mattybrad/drumkid/docs/v6/photos/monochrome/IMG_20201204_124251521.jpg

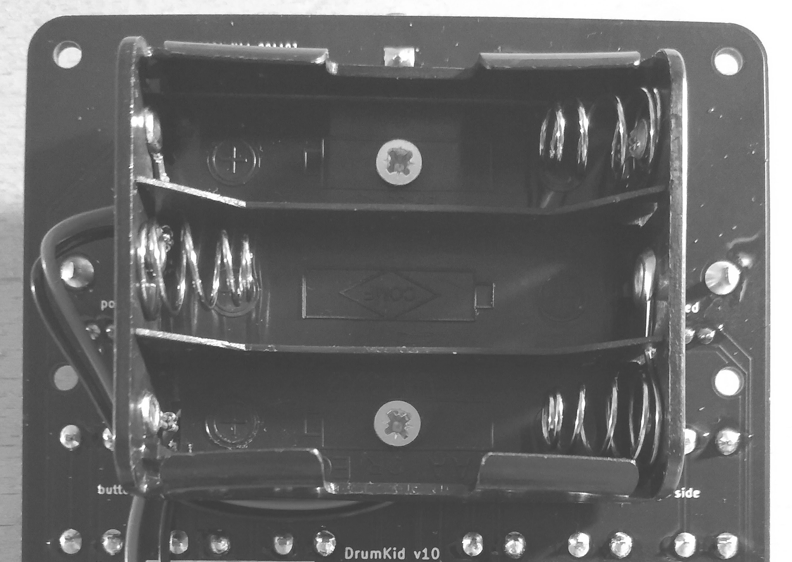
docs/v6/photos/monochrome/IMG_20201204_124251521.jpg
