mattybrad/drumkid/docs/v6/photos/monochrome/IMG_20201204_130344814.jpg

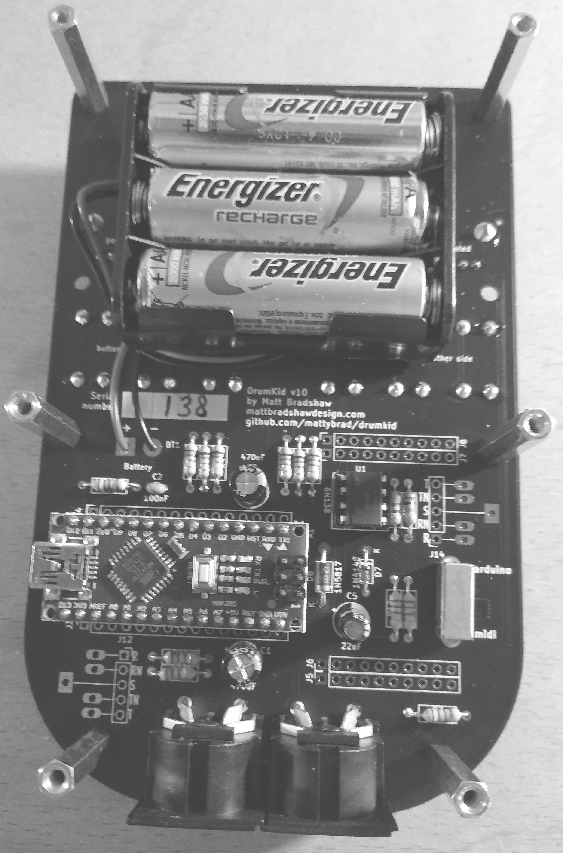
docs/v6/photos/monochrome/IMG_20201204_130344814.jpg
