mattybrad/drumkid/docs/v6/photos/monochrome/IMG_20201204_140902341.jpg

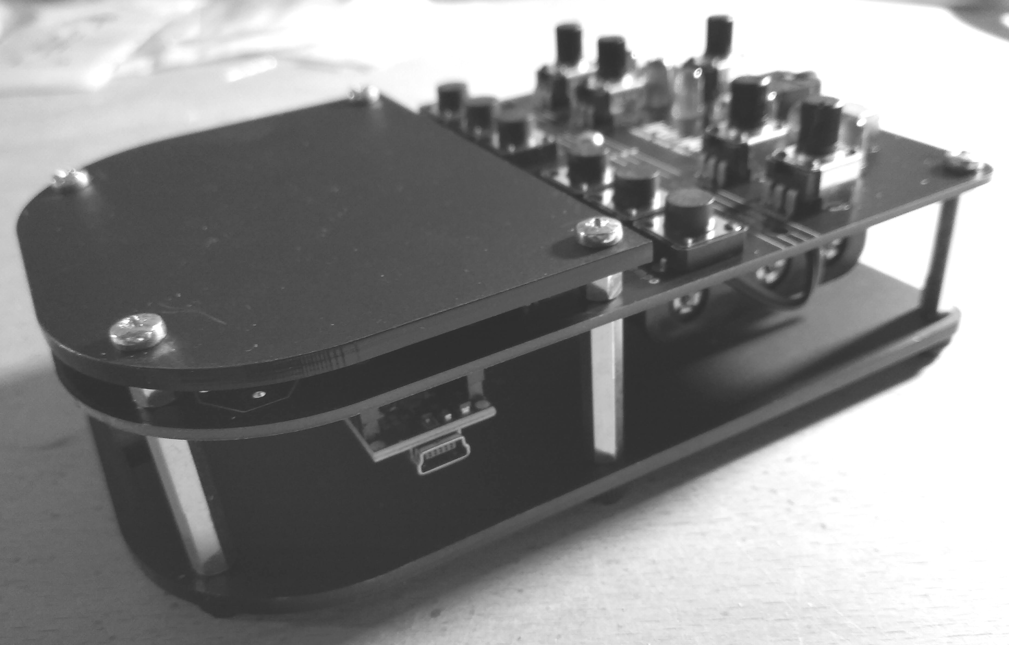
docs/v6/photos/monochrome/IMG_20201204_140902341.jpg
