mattybrad/drumkid/misc/jig/underside.png

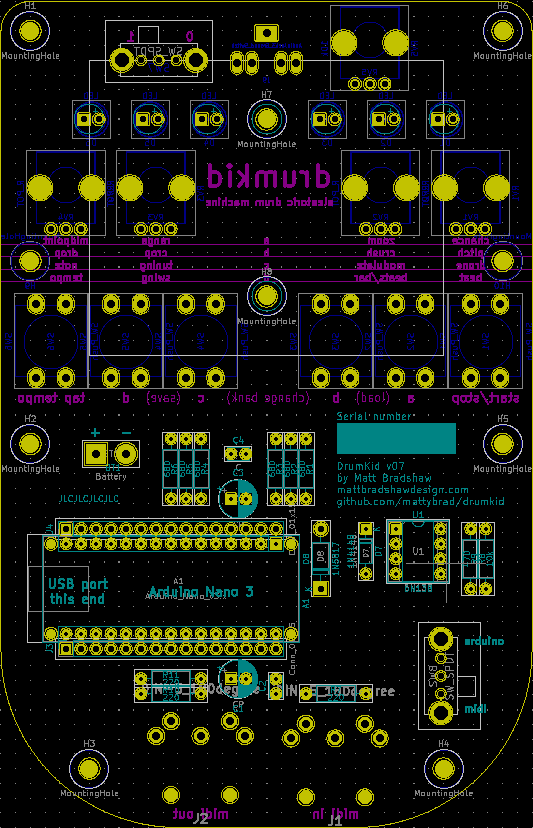
misc/jig/underside.png
