mattybrad/drumkid/case/drumkid_v3_cover.stl

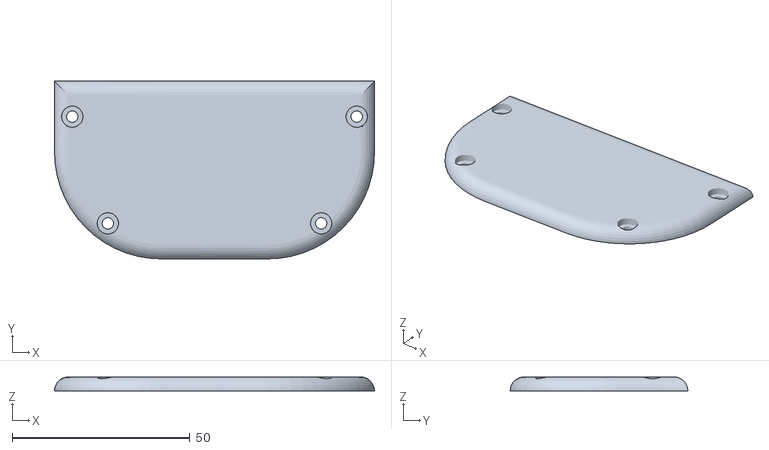
[picture p23: CAD file, 2019-08-09]
case/drumkid_v3_cover.stl
90.0 x 50.0 x 4.00
