mattybrad/drumkid/case/v6/drumkid laser parts.dxf

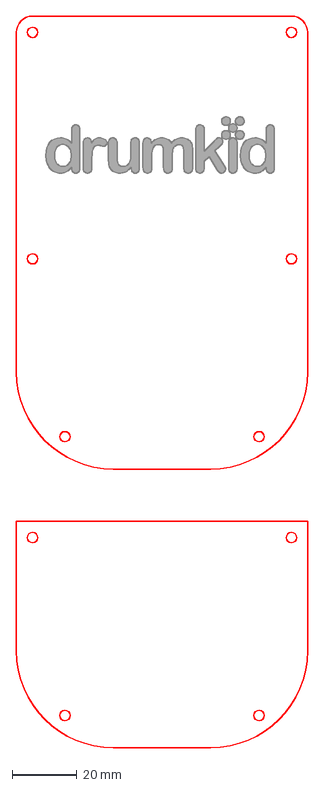
[picture p24: CAD file, 2021-01-12]
case/v6/drumkid laser parts.dxf
90.0 x 226.2 mm
