mattybrad/drumkid/case/drumkid laser parts v2.dxf

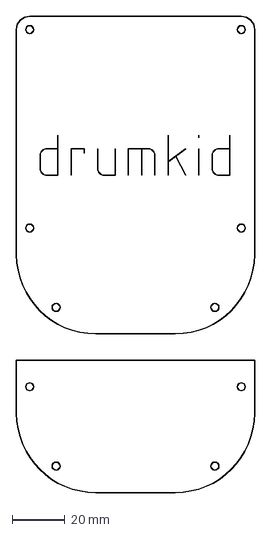
[picture p25: CAD file, 2019-08-09]
case/drumkid laser parts v2.dxf
90.0 x 180.0 mm
