mattybrad/drumkid/case/v6/drumkid laser parts 600x600.dxf

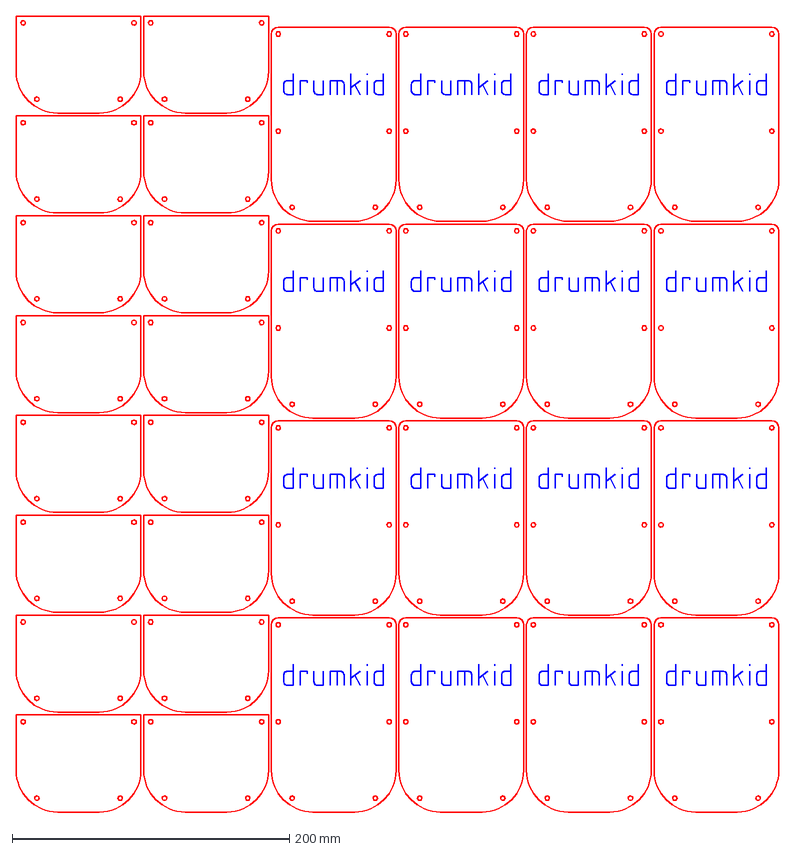
[picture p26: CAD file, 2020-04-07]
case/v6/drumkid laser parts 600x600.dxf
550.0 x 574.0 mm
