mattybrad/drumkid/case/v3 cover.FCStd

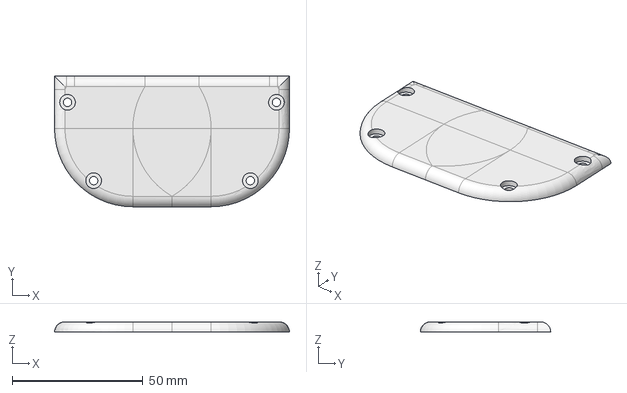
[picture p27: CAD file, 2019-08-09]
case/v3 cover.FCStd
90.0 x 50.0 x 4.00 mm
