mattybrad/drumkid/misc/jig/jig_underside.FCStd

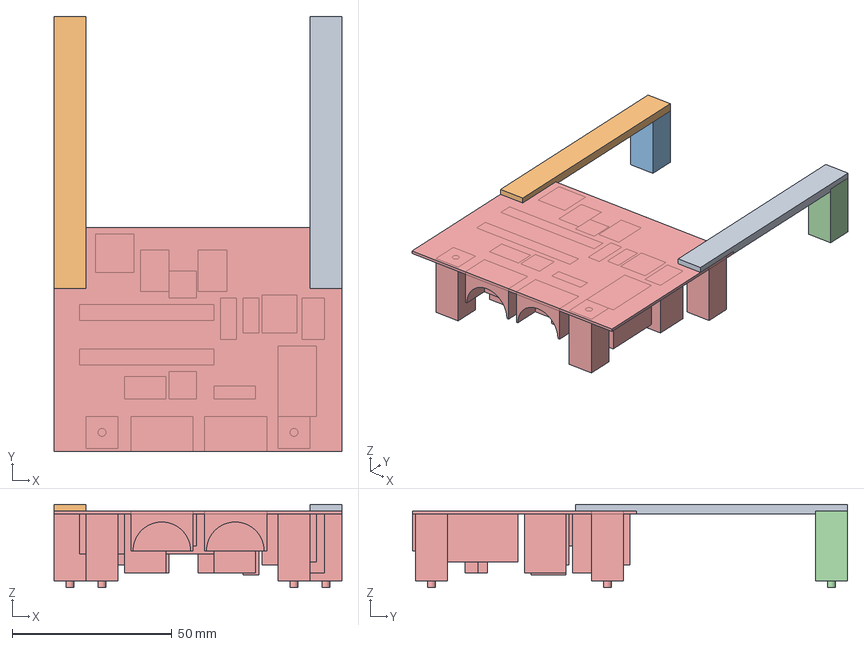
[picture p28: CAD file, 2020-06-18]
misc/jig/jig_underside.FCStd
90.0 x 136.0 x 26.0 mm
