mattybrad/drumkid/case/drumkid cover laser 2.dxf

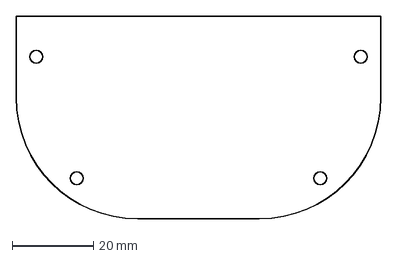
[picture p29: CAD file, 2019-08-09]
case/drumkid cover laser 2.dxf
90.0 x 50.0 mm
