mattybrad/drumkid/case/drumkid cover laser 1.dxf

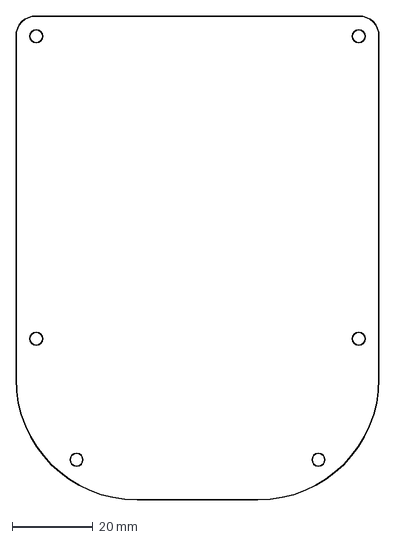
[picture p30: CAD file, 2019-08-09]
case/drumkid cover laser 1.dxf
90.0 x 120.0 mm
