mattybrad/drumkid/case/drumkid_case_bottom.stl

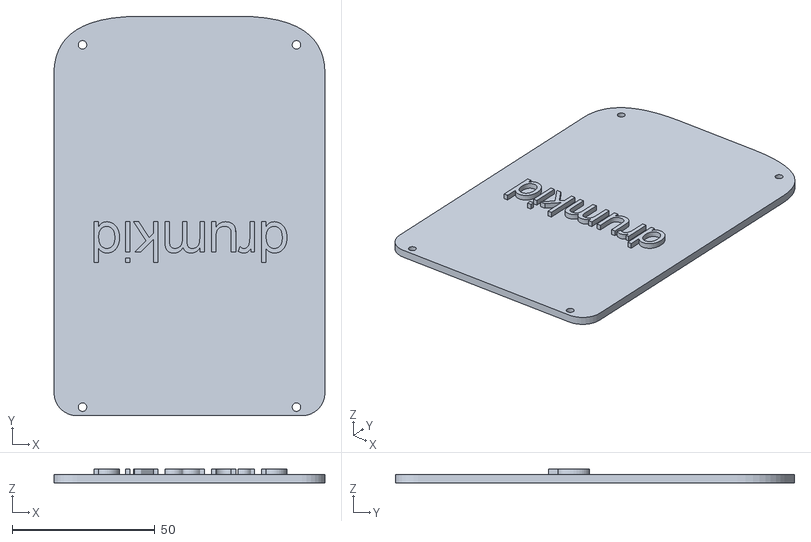
[picture p31: CAD file, 2019-08-09]
case/drumkid_case_bottom.stl
95.0 x 140.0 x 5.00
