mattybrad/drumkid/misc/jig/jig9.stl

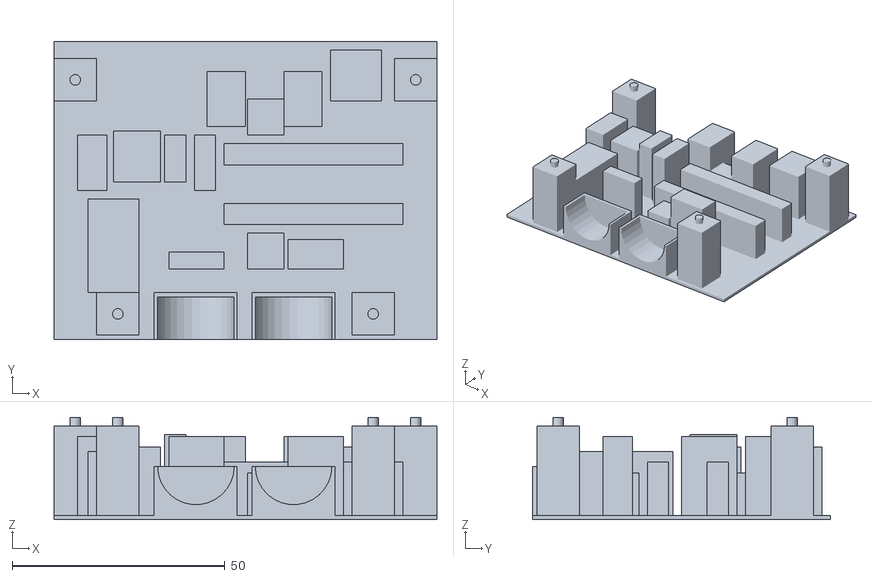
[picture p32: CAD file, 2020-06-18]
misc/jig/jig9.stl
90.0 x 70.0 x 24.0
