mattybrad/drumkid/case/drumkid_knob_small.stl

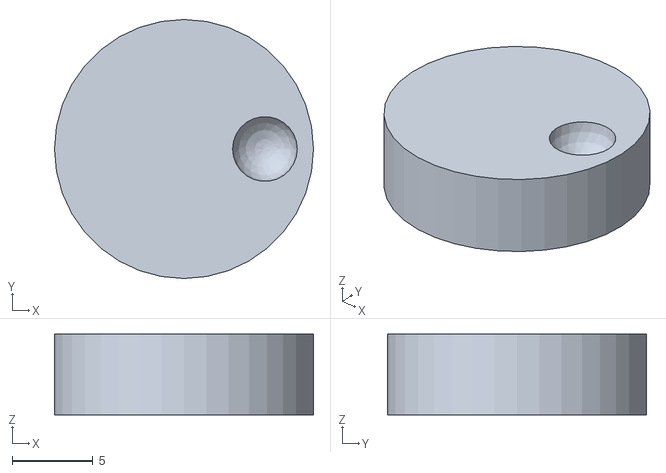
[picture p33: CAD file, 2019-08-09]
case/drumkid_knob_small.stl
16.0 x 16.0 x 5.00
