mattybrad/drumkid/arduino/eeprom_writer/eeprom_writer.ino

// This sketch will overwrite your stored Drumkid beats/settings
// PLEASE MAKE SURE YOU HAVE BACKED UP YOUR DRUMKID USING THE EEPROM_READER SKETCH FIRST!

#include <EEPROM.h>

// paste your settings from eeprom_reader between the brackets below
// (delete existing numbers, shown only as an example)
byte drumkidData[1024] = {
  105,127,28,159,4,166,241,128,180,26,127,141,157,64,162,212,
  255,255,255,255,255,255,255,255,134,108,124,142,91,171,247,148,
  127,127,127,169,156,41,152,72,255,255,255,255,255,255,255,255,
  183,166,124,95,239,162,211,203,127,127,127,252,70,64,117,144,
  255,255,255,255,255,255,255,255,67,109,111,165,190,223,177,90,
  172,127,127,122,92,242,110,139,255,255,255,255,255,255,255,255,
  118,143,88,117,221,172,148,128,145,127,127,227,198,222,94,147,
  255,255,255,255,255,255,255,255,78,101,106,90,25,248,240,128,
  127,127,127,208,27,64,64,198,255,255,255,255,255,255,255,255,
  92,162,76,107,204,170,240,128,127,127,127,251,230,64,212,74,
  255,255,255,255,255,255,255,255,103,122,8,161,192,240,204,128,
  127,127,127,142,213,64,165,96,255,255,255,255,255,255,255,255,
  92,157,79,175,221,160,146,128,127,127,127,159,181,30,91,97,
  255,255,255,255,255,255,255,255,90,144,91,170,216,215,135,128,
  127,127,127,178,129,64,78,157,255,255,255,255,255,255,255,255,
  108,128,44,153,241,219,165,128,127,181,127,121,107,64,47,123,
  255,255,255,255,255,255,255,255,98,147,88,136,155,215,214,128,
  127,127,127,224,153,64,134,89,255,255,255,255,255,255,255,255,
  86,112,68,188,247,194,138,49,127,127,127,175,167,93,97,251,
  255,255,255,255,255,255,255,255,110,148,73,184,86,174,254,225,
  127,110,127,229,195,64,245,114,255,255,255,255,255,255,255,255,
  78,139,31,116,96,177,158,128,110,127,127,243,133,64,233,96,
  255,255,255,255,255,255,255,255,123,124,56,186,155,254,130,35,
  179,127,127,20,117,64,233,101,255,255,255,255,255,255,255,255,
  174,143,76,114,85,247,204,128,127,127,127,168,201,84,116,130,
  255,255,255,255,255,255,255,255,139,144,43,124,222,242,137,128,
  127,127,127,168,162,252,8,153,255,255,255,255,255,255,255,255,
  114,149,108,114,233,170,168,128,127,87,127,161,141,64,123,132,
  255,255,255,255,255,255,255,255,151,110,67,189,255,194,176,128,
  159,127,127,82,93,64,180,140,255,255,255,255,255,255,255,255,
  156,162,11,181,149,171,183,128,187,127,127,136,194,64,71,130,
  255,255,255,255,255,255,255,255,124,101,97,132,156,160,243,128,
  131,127,127,47,206,64,97,96,255,255,255,255,255,255,255,255,
  191,152,50,123,61,204,128,128,127,127,127,127,63,64,93,5,
  255,255,255,255,255,255,255,255,88,117,114,90,191,161,199,128,
  127,127,127,224,18,64,247,134,255,255,255,255,255,255,255,255,
  135,126,119,108,147,187,140,221,127,179,127,16,97,64,227,112,
  255,255,255,255,255,255,255,255,183,126,59,90,194,161,191,128,
  127,127,127,78,212,64,107,153,255,255,255,255,255,255,255,255,
  78,181,99,91,92,231,147,156,127,127,127,170,138,64,187,20,
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
};

void setup() {
  // initialize serial and wait for port to open:
  Serial.begin(9600);
  while (!Serial) {
    ; // wait for serial port to connect. Needed for native USB port only
  }
  Serial.println("writing drumkid data...");
  for(int i=0; i<1024; i++) {
    EEPROM.write(i, drumkidData[i]);
  }
  Serial.println("done");
}

void loop() {
  // nothing in loop, don't want program to run repeatedly and wear out the EEPROM
}
