mattybrad/drumkid/arduino/1.1/drumkid/clap.h

#ifndef clap_H_
#define clap_H_
 
#if ARDUINO >= 100
#include "Arduino.h"
#else
#include "WProgram.h"
#endif
#include "src/MozziDK/src/mozzi_pgmspace.h"
 
#define clap_NUM_CELLS 2751
#define clap_SAMPLERATE 16384
 
CONSTTABLE_STORAGE(int8_t) clap_DATA [] = {2, -1, 2, -2, 2, 6, 8, 10, -14, 15,
11, 45, 35, -7, -12, -19, -35, -50, -36, -28, -2, 5, 5, 23, 23, 14, 41, 18, 10,
-1, 5, -1, -27, -22, -18, -5, -22, -15, 2, 3, 18, 36, 21, 19, -6, -6, -25, -25,
-23, -36, -3, 3, 8, 19, 28, 23, 14, 6, 3, -11, -4, -3, -12, -2, -5, -13, -12,
-8, -2, 1, 19, 10, -2, 1, -5, 3, 9, -5, -10, -10, -9, 1, -2, 14, 10, 5, -1, 1,
-2, -12, -11, -2, 4, 0, -2, -4, 10, 8, 7, 2, 3, 2, -3, -6, -6, -1, -2, -4, -2,
-1, -2, 4, 1, 3, 3, -3, -3, -3, 3, 4, 3, 3, 0, -5, -1, 5, 2, 0, -3, -3, -1, -1,
3, -1, -3, 2, 0, 0, -2, 0, 0, -2, 3, 3, 2, 0, -5, -3, 4, 4, 0, -1, 0, 0, -1, -1,
1, 1, -2, -2, 1, 2, 2, -1, -2, -2, -2, 2, 1, 2, 0, 1, -1, -1, 1, 1, -3, 1, 1, 0,
6, -31, 18, 38, 46, 30, -24, -18, -33, -27, -31, -21, -12, -26, 6, 29, 33, 16,
-4, 14, -26, -20, 10, 18, 32, 28, 9, -9, -18, -15, -20, -48, 1, 14, 5, 12, 20,
45, 28, -20, -23, -17, -27, -16, -11, -6, 20, 35, 21, -14, -22, -24, -8, 7, 2,
42, 24, 6, -1, -5, -20, -28, -5, -13, -9, -2, 15, 14, -4, 8, 23, 15, 9, -7, -11,
-16, -22, -16, -7, -12, -7, 13, 20, 24, 24, 12, 0, 5, -8, -20, -11, -4, -7, -10,
-10, -4, -2, 16, 15, 6, 9, 1, 5, -8, -14, -9, -4, -6, -3, 4, 8, 4, 8, 13, 7, 0,
-10, -10, -11, -7, 2, 1, 0, 0, 9, 9, 1, 0, 2, 3, 2, 0, -6, -7, -4, 0, -1, 2, -2,
-2, 1, 2, 1, 1, 3, -2, -5, -2, -3, 4, 10, 6, 7, 0, -3, -4, -1, -4, -4, -6, -5,
1, 0, 4, 4, 7, 0, -3, -2, -5, 3, 0, 2, 4, 2, 2, -1, -4, -4, -1, 3, 2, 0, -3, 0,
0, 0, -3, 2, -2, -3, -2, 0, 0, 3, 0, 0, 0, 0, 2, -4, 3, -7, 5, -1, 16, 19, 31,
22, -30, -19, 1, -38, -30, 2, -16, -23, 15, 13, -21, 18, 8, 12, -5, 6, 54, 42,
37, -17, -40, -34, -54, -40, -20, -12, 0, 27, 37, 43, 51, 39, 0, -32, -37, -6,
22, -1, -6, -29, -29, -13, 14, 10, -11, -4, -7, -13, -2, 15, 23, 18, 9, 6, 1,
-2, -5, 18, 7, -3, -19, 1, -6, -33, -5, 4, 9, 1, -4, -5, 11, 15, 2, 4, -1, -16,
-8, 20, 9, -3, 0, 10, 16, 2, -17, -21, -24, 1, 5, -3, -6, -8, 8, 1, 15, 21, 13,
0, -4, -1, 3, -11, -6, -12, -4, 12, 16, 20, 9, -14, -37, -57, -61, -1, 30, 38,
57, 74, 42, -21, -50, -26, -56, -6, 25, 10, 23, -1, 11, 27, 30, -11, -26, -32,
-17, -17, -16, -23, 7, -4, -10, 53, 50, 37, 41, 10, -14, 18, -36, -51, -53, -63,
-19, -11, 18, 11, 47, 38, 24, 46, 10, -7, -24, -38, -22, -17, -19, 13, -8, 29,
57, 1, -2, -9, -42, 2, -39, -23, 42, 21, 11, -17, 25, 33, -6, -30, 0, -21, -8,
16, -14, 5, 21, 1, -38, -16, 22, 33, -5, -29, -1, 35, 22, 13, 13, -32, -30, 19,
9, -36, -24, -32, -6, 23, 44, 41, 26, 30, 12, 7, -45, -24, -28, -21, -11, -29,
-3, 12, 32, 28, -8, -11, -1, -16, -2, -12, -29, -11, 55, 53, 19, -7, -15, 11,
-23, -27, 33, 24, 0, -4, -31, 2, 8, -5, -35, -33, -31, -11, 30, 4, 43, 42, 42,
23, -27, -29, -45, -23, 17, -7, -26, -16, 9, 5, 20, 52, 33, 13, -9, -7, -13,
-25, -28, -24, -12, 1, 16, 25, 49, 39, -6, -32, -33, -16, -15, -15, -15, -11,
12, 15, 16, 9, -5, -16, 18, 23, -7, 12, -13, -27, 21, 32, 6, 2, -11, -9, -4,
-21, -6, -2, -6, -30, -23, -4, 22, 33, 43, 59, 40, 10, -46, -64, -45, 2, 0, 0,
-12, -25, 1, -16, -12, 35, 24, 47, 28, -7, 21, 0, -7, -18, -13, 8, -5, -30, -20,
-27, -11, 10, 25, -14, -7, 10, -3, 25, 12, 6, 11, 10, -1, 5, -5, -18, -17, 6, 5,
-18, 7, 18, 13, 37, 2, -24, -25, -14, 3, -16, -1, -15, -8, 27, 18, 1, -1, -21,
-12, 13, 8, 5, 8, 6, 6, 5, 6, -10, -36, -4, 8, 17, -4, 7, 10, -19, 8, -14, -7,
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

#endif /* clap_H_ */
