mattybrad/drumkid/arduino/1.1/drumkid/kick.h

#ifndef kick_H_
#define kick_H_
 
#if ARDUINO >= 100
#include "Arduino.h"
#else
#include "WProgram.h"
#endif
#include "src/MozziDK/src/mozzi_pgmspace.h"
 
#define kick_NUM_CELLS 7581
#define kick_SAMPLERATE 16384
 
CONSTTABLE_STORAGE(int8_t) kick_DATA [] = {0, 2, 18, 33, 44, 53, 62, 69, 75, 81,
86, 89, 93, 95, 98, 100, 101, 101, 98, 94, 88, 84, 77, 70, 65, 58, 51, 44, 37,
30, 22, 14, 6, -1, -8, -16, -23, -31, -37, -45, -51, -58, -65, -71, -77, -83,
-88, -94, -100, -103, -108, -112, -115, -119, -123, -126, -127, -127, -128,
-128, -128, -127, -125, -126, -125, -124, -123, -122, -121, -119, -116, -113,
-112, -107, -104, -101, -97, -94, -89, -84, -79, -74, -69, -63, -58, -52, -47,
-40, -33, -28, -21, -14, -9, -4, 1, 6, 10, 14, 18, 21, 24, 27, 30, 33, 35, 37,
39, 41, 44, 46, 47, 48, 51, 51, 53, 54, 55, 58, 58, 60, 61, 61, 63, 64, 65, 66,
66, 67, 68, 69, 69, 70, 71, 71, 72, 71, 72, 72, 73, 73, 73, 73, 74, 73, 73, 74,
73, 74, 74, 73, 73, 73, 72, 72, 72, 72, 72, 71, 71, 70, 70, 69, 69, 68, 68, 66,
66, 65, 64, 64, 63, 63, 61, 60, 60, 60, 57, 57, 57, 55, 55, 53, 52, 51, 50, 49,
47, 47, 46, 44, 43, 41, 41, 39, 37, 37, 36, 34, 33, 31, 30, 29, 27, 26, 25, 24,
22, 20, 18, 18, 16, 14, 12, 11, 10, 8, 6, 5, 3, 1, 0, -1, -3, -5, -8, -9, -12,
-13, -15, -17, -19, -21, -23, -26, -28, -30, -32, -34, -35, -38, -40, -42, -45,
-48, -49, -51, -54, -56, -58, -61, -62, -65, -68, -69, -71, -74, -76, -78, -81,
-83, -85, -87, -88, -90, -92, -94, -96, -98, -100, -101, -102, -104, -106, -107,
-109, -110, -112, -112, -113, -114, -116, -117, -118, -118, -119, -119, -121,
-121, -121, -122, -122, -122, -122, -123, -122, -122, -121, -122, -121, -120,
-120, -119, -117, -117, -116, -115, -112, -111, -110, -108, -106, -104, -103,
-101, -98, -96, -94, -91, -88, -88, -85, -82, -80, -77, -74, -72, -69, -66, -64,
-61, -58, -56, -53, -50, -47, -44, -42, -39, -35, -34, -31, -28, -25, -22, -20,
-18, -15, -12, -10, -6, -3, -1, 2, 3, 6, 9, 12, 14, 16, 19, 21, 23, 26, 27, 30,
33, 35, 37, 39, 42, 43, 47, 49, 50, 52, 53, 56, 57, 60, 62, 63, 65, 67, 68, 70,
71, 74, 75, 77, 78, 79, 81, 83, 83, 85, 87, 87, 89, 90, 91, 92, 93, 94, 95, 96,
97, 98, 99, 100, 100, 101, 102, 102, 104, 103, 104, 105, 104, 106, 105, 106,
105, 106, 106, 107, 106, 107, 107, 107, 106, 106, 106, 106, 106, 106, 106, 106,
104, 104, 104, 103, 103, 102, 101, 101, 101, 100, 99, 98, 97, 96, 96, 94, 94,
92, 91, 91, 90, 89, 87, 86, 85, 83, 82, 81, 80, 79, 77, 76, 73, 73, 71, 70, 68,
67, 66, 64, 62, 61, 59, 57, 56, 54, 52, 51, 48, 47, 45, 43, 42, 39, 37, 36, 34,
32, 31, 28, 27, 25, 23, 21, 19, 18, 15, 14, 11, 10, 7, 6, 3, 2, -1, -3, -4, -8,
-9, -11, -14, -15, -18, -20, -22, -25, -26, -29, -31, -33, -35, -37, -40, -42,
-45, -47, -48, -51, -54, -56, -57, -60, -62, -64, -66, -69, -71, -73, -75, -77,
-79, -82, -83, -86, -87, -89, -91, -93, -95, -96, -98, -100, -102, -103, -104,
-106, -107, -108, -111, -111, -113, -113, -114, -116, -117, -117, -117, -119,
-119, -119, -120, -120, -121, -121, -121, -122, -122, -120, -121, -120, -120,
-120, -119, -119, -119, -118, -117, -117, -116, -115, -114, -113, -112, -110,
-109, -108, -106, -104, -103, -101, -100, -99, -97, -95, -92, -91, -89, -87,
-85, -83, -81, -78, -76, -73, -71, -69, -67, -64, -62, -59, -56, -54, -52, -49,
-48, -45, -42, -40, -37, -34, -33, -29, -28, -25, -22, -20, -19, -16, -13, -11,
-8, -6, -4, -1, 0, 3, 5, 7, 9, 11, 13, 17, 18, 21, 22, 25, 27, 28, 30, 33, 34,
36, 38, 39, 42, 43, 45, 48, 50, 51, 52, 55, 55, 58, 59, 60, 63, 64, 66, 66, 69,
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

#endif /* kick_H_ */
