mattybrad/drumkid/arduino/1.1/drumkid/snare.h

#ifndef snare_H_
#define snare_H_
 
#if ARDUINO >= 100
#include "Arduino.h"
#else
#include "WProgram.h"
#endif
#include "src/MozziDK/src/mozzi_pgmspace.h"
 
#define snare_NUM_CELLS 2840
#define snare_SAMPLERATE 16384
 
CONSTTABLE_STORAGE(int8_t) snare_DATA [] = {2, -2, 9, 17, -13, -24, -21, -8, 3,
11, 12, 12, 18, 12, 6, 3, 4, 1, -2, -11, -13, -9, -18, -21, -21, -17, -11, -6,
6, 10, 3, -3, -2, 11, 23, 21, 11, -1, -6, -10, -7, 1, 5, 8, 15, 17, 21, 22, 13,
14, 18, 22, 15, 8, -1, -5, -9, -30, -24, -11, -26, -9, -7, -25, -10, -3, -24,
-14, 13, -15, -31, -13, -18, -18, -17, -13, -4, -2, -5, -4, -11, -31, -8, 25,
12, 0, -1, -23, -20, 17, 40, 35, 19, 28, 40, 37, 27, 24, 18, 17, 15, 9, 9, 9,
-14, -23, -14, -2, 4, -17, -12, -9, -18, -5, 3, 9, 16, 19, 21, 25, 23, 12, 5, 5,
6, -13, -2, 6, -13, -31, -16, 0, -2, 25, 17, 23, 45, 29, 26, 31, 1, -7, 8, 37,
4, -10, 20, -19, -35, -54, -64, -56, -42, -19, -24, -15, -28, -67, -80, -61,
-63, -38, -6, -70, -110, -62, -33, -87, -102, -35, -6, -81, -76, 6, 5, -29, -33,
-10, 18, 32, 22, 34, 43, 45, 47, 42, 53, 48, 43, 44, 26, 43, 46, 33, 44, 51, 28,
19, 44, 55, 47, 38, 40, 44, 44, 29, 31, 29, 22, 24, 40, 41, 34, 41, 51, 24, -7,
7, 41, 14, -32, 23, 32, 26, 19, -2, 26, 27, 4, 24, 39, -48, -101, -60, -1, 4,
-47, 2, 8, -46, -61, -52, -44, -83, -88, -91, -87, -90, -108, -92, -58, -80,
-101, -83, -83, -55, -65, -92, -85, -89, -22, -35, -90, -77, -82, -72, -59, -29,
20, 5, -59, -38, 3, 36, -9, -30, 28, 43, 35, 41, 28, 35, 64, 59, 51, 43, 56, 64,
60, 53, 65, 66, 56, 51, 54, 68, 55, 46, 64, 70, 60, 44, 56, 64, 51, 42, 36, 40,
48, 60, 40, 41, 40, 25, -6, 12, 42, 14, -8, -2, 26, 56, 5, -50, 16, 34, -15,
-54, -47, 3, 25, -33, -51, -11, 17, -40, -101, -25, 25, -48, -99, -57, -26, -37,
-65, -63, -75, -63, -70, -75, -55, -66, -76, -80, -76, -68, 9, -5, -66, -39,
-10, -11, -42, -58, -2, -23, -76, -33, -23, -37, 10, 45, -1, -18, -28, 16, 43,
27, 12, 28, 36, -5, 35, 42, 20, 27, 49, 61, 46, 54, 56, 39, 48, 18, 23, 46, 48,
40, 36, 46, 36, 1, -12, 53, 29, 6, -12, 0, 29, -17, -2, 14, 10, -35, -26, 43,
58, 6, -29, 29, -16, -49, -5, 1, 37, 27, -3, -16, -21, 31, 33, -8, 9, 20, -9,
-11, -13, 4, 42, -7, -2, 25, 8, 8, 3, 33, 12, -33, -2, 28, 8, -23, 11, 34, 8,
25, 7, 10, 25, 33, 21, 1, 26, 12, 24, 20, 20, 12, 0, -11, -11, 45, 10, -2, 18,
32, 26, 8, 6, 10, 40, 27, 10, 6, 43, -9, -20, 34, 9, 9, 29, 47, 16, -18, -11,
13, 31, 12, 3, 14, -4, 6, 0, -19, 19, 14, 16, 12, -21, -7, -8, -4, 3, -18, 6, 3,
-40, -17, -10, -22, -23, -4, -9, -39, -29, 7, -24, -65, -40, -4, 0, -28, -28,
-26, -15, -12, -28, -41, -14, -35, -37, -25, -26, -4, -5, 6, 2, -26, -8, 23, 9,
9, -16, 13, 33, 13, 3, -15, 2, 8, -8, 10, 16, 10, 45, 27, 9, 12, 2, 17, 40, 9,
-4, 9, -9, 25, 35, 5, 20, 42, 38, -5, -28, 12, 8, 24, 40, 18, 14, 27, 22, -2,
24, 26, 14, 6, 15, 31, 23, 13, 5, 3, 17, 36, -2, -4, 10, 4, 17, 16, -5, 7, 13,
2, 6, -7, -4, 2, 7, 6, 5, 3, 0, 4, 5, 5, -9, -17, 8, 16, 11, 3, -4, 11, 18, 15,
0, 4, 8, 11, 3, 12, 23, 11, 11, 8, 4, -7, 0, -8, 12, 16, 6, 18, 8, -7, 9, 30,
-16, -19, 1, 5, -1, -5, 8, 1, -17, -14, -1, -4, -6, -10, -9, -4, 2, -4, -5, -4,
-21, -26, 5, -3, -11, -2, -9, -12, -10, 5, -12, -33, -17, 4, -3, -18, -9, 4, 2,
-5, -4, -13, -7, -5, 9, 5, -17, -9, -5, 1, -5, -10, -12, -5, 6, 1, -4, 3, 1,
-10, 5, 9, 7, 1, 8, 14, 3, 4, 10, 7, 1, 10, 16, 8, 2, 7, 5, 11, 12, 1, 4, 8, 18,
10, -2, 8, 8, 11, 14, 2, 3, 8, 10, 12, 10, 12, 4, 1, 9, 13, 7, -4, 0, 10, 13, 5,
9, 14, 11, 17, 5, 4, 9, 4, 10, 6, 0, 4, 6, 6, -1, 1, 14, 7, -3, -6, 5, 6, -1, 4,
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

#endif /* snare_H_ */
