mattybrad/drumkid/arduino/1.1/drumkid/tom.h

#ifndef tom_H_
#define tom_H_
 
#if ARDUINO >= 100
#include "Arduino.h"
#else
#include "WProgram.h"
#endif
#include "src/MozziDK/src/mozzi_pgmspace.h"
 
#define tom_NUM_CELLS 2870
#define tom_SAMPLERATE 16384
 
CONSTTABLE_STORAGE(int8_t) tom_DATA [] = {0, -1, 0, 0, 0, 0, 1, 4, 6, 5, 4, 4,
2, 3, -83, -128, -104, -78, -57, -55, -47, -50, -47, -40, -34, -30, -22, -16,
-8, -1, 6, 13, 20, 26, 31, 37, 42, 46, 50, 54, 56, 58, 59, 61, 60, 60, 57, 52,
54, 54, 51, 48, 47, 47, 46, 46, 46, 45, 45, 45, 44, 44, 44, 43, 44, 43, 42, 42,
42, 42, 42, 41, 41, 41, 40, 40, 40, 40, 36, 31, 32, 32, 34, 35, 35, 30, 24, 24,
26, 28, 28, 19, 16, 19, 21, 20, 12, 11, 14, 16, 9, 5, 8, 9, 3, 0, 4, 3, -4, -4,
-1, -5, -10, -7, -7, -13, -14, -11, -14, -19, -17, -15, -22, -23, -20, -23, -28,
-25, -24, -31, -31, -28, -31, -36, -33, -33, -38, -40, -35, -37, -42, -42, -38,
-40, -45, -46, -42, -41, -47, -49, -47, -44, -44, -51, -52, -49, -46, -45, -51,
-55, -52, -49, -47, -47, -46, -52, -53, -52, -49, -48, -48, -47, -46, -47, -46,
-46, -45, -44, -44, -45, -49, -50, -47, -42, -40, -39, -40, -41, -41, -41, -41,
-41, -40, -41, -40, -39, -34, -29, -31, -32, -31, -24, -23, -24, -18, -17, -15,
-11, -10, -6, -4, -1, 2, 5, 7, 11, 14, 16, 19, 21, 24, 27, 29, 30, 33, 35, 37,
39, 39, 42, 42, 43, 46, 45, 48, 48, 45, 48, 50, 48, 45, 47, 51, 51, 48, 46, 45,
44, 43, 47, 52, 51, 48, 47, 45, 45, 44, 43, 44, 43, 43, 44, 42, 42, 41, 42, 41,
36, 31, 32, 33, 35, 35, 35, 36, 36, 35, 30, 24, 24, 27, 28, 29, 28, 21, 18, 19,
22, 22, 19, 13, 14, 16, 17, 12, 8, 9, 11, 8, 3, 4, 7, 4, -1, -1, 1, -1, -6, -5,
-4, -7, -10, -9, -8, -12, -15, -12, -14, -18, -17, -16, -20, -22, -21, -21, -24,
-26, -24, -24, -29, -30, -27, -29, -33, -33, -30, -31, -35, -36, -34, -33, -37,
-39, -38, -35, -37, -41, -42, -41, -38, -37, -41, -44, -44, -42, -39, -38, -41,
-46, -47, -45, -42, -42, -40, -40, -39, -39, -43, -48, -46, -45, -43, -41, -41,
-40, -40, -40, -39, -39, -39, -39, -39, -39, -37, -38, -38, -35, -31, -27, -29,
-29, -31, -32, -31, -26, -22, -21, -23, -21, -17, -17, -15, -11, -10, -7, -6,
-3, -2, 1, 4, 6, 9, 11, 14, 16, 18, 21, 23, 24, 26, 28, 29, 31, 32, 34, 36, 37,
38, 38, 40, 40, 40, 41, 44, 43, 40, 43, 45, 45, 44, 41, 40, 43, 47, 46, 45, 43,
42, 42, 40, 39, 40, 40, 39, 39, 38, 39, 38, 39, 37, 38, 37, 37, 37, 37, 36, 37,
35, 35, 34, 30, 26, 25, 27, 28, 29, 30, 29, 25, 21, 19, 21, 22, 23, 20, 16, 15,
15, 17, 16, 13, 10, 11, 12, 11, 7, 5, 7, 6, 3, 2, 2, 3, 0, -2, -3, -2, -4, -7,
-7, -7, -8, -10, -10, -10, -12, -14, -13, -14, -16, -17, -17, -18, -21, -21,
-21, -21, -24, -25, -25, -24, -26, -28, -28, -27, -28, -30, -32, -30, -29, -31,
-34, -34, -33, -31, -32, -35, -37, -36, -34, -33, -35, -37, -40, -38, -36, -35,
-34, -33, -36, -39, -40, -40, -38, -37, -35, -34, -35, -35, -34, -34, -33, -34,
-33, -32, -33, -33, -32, -32, -32, -32, -31, -30, -31, -31, -31, -30, -30, -28,
-24, -22, -21, -22, -23, -20, -17, -16, -16, -14, -12, -10, -8, -7, -5, -3, -1,
1, 3, 4, 7, 8, 11, 13, 15, 17, 18, 20, 22, 23, 25, 26, 29, 29, 31, 32, 33, 33,
35, 35, 36, 37, 36, 37, 38, 39, 38, 36, 37, 40, 41, 41, 38, 37, 37, 36, 35, 35,
36, 39, 42, 42, 41, 39, 38, 37, 37, 37, 36, 36, 35, 36, 33, 30, 27, 27, 27, 29,
28, 29, 29, 30, 29, 28, 28, 24, 21, 20, 21, 22, 23, 23, 19, 17, 16, 15, 17, 18,
14, 12, 12, 11, 12, 10, 9, 7, 7, 7, 5, 4, 4, 3, 2, 0, -1, -1, -1, -4, -5, -5,
-5, -7, -8, -8, -9, -10, -12, -12, -12, -13, -15, -16, -16, -17, -18, -18, -19,
-19, -20, -22, -21, -21, -23, -24, -25, -24, -24, -26, -27, -28, -27, -26, -29,
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

#endif /* tom_H_ */
