mattybrad/drumkid/arduino/1.1/drumkid/closedhat.h

#ifndef closedhat_H_
#define closedhat_H_
 
#if ARDUINO >= 100
#include "Arduino.h"
#else
#include "WProgram.h"
#endif
#include "src/MozziDK/src/mozzi_pgmspace.h"
 
#define closedhat_NUM_CELLS 1527
#define closedhat_SAMPLERATE 16384
 
CONSTTABLE_STORAGE(int8_t) closedhat_DATA [] = {0, 2, -2, 6, -2, -2, 0, -3, -2,
7, -7, 3, 6, -5, -4, 9, -6, 4, -3, -10, 23, -17, 0, 6, -14, 19, -19, 9, 4, -20,
23, -20, 8, -6, 2, 3, -2, -1, -4, 7, -7, 3, 0, -4, 1, 4, -8, 12, -7, -2, 5, -5,
3, -1, -5, 8, -6, -1, 0, 12, -18, 8, -3, -2, 6, -12, 14, -20, 16, -8, -11, 16,
-4, -14, 24, -25, 18, -14, -11, 47, -41, 20, -10, -2, 15, -14, -6, 10, 1, -20,
36, -51, 41, -17, -19, 36, -59, 45, -40, 13, 8, -21, -5, 13, 2, -29, 44, -36,
16, -10, 6, 5, -44, 45, -46, 20, -5, -6, -5, 13, 9, -31, 31, -34, 38, -42, 0,
-4, -36, 36, -31, 12, -13, 20, -17, -4, 31, -50, 27, -20, 11, -23, 24, 5, -31,
24, -9, -3, -3, 21, -39, 45, -32, 6, 10, -5, -1, -16, 25, -29, 19, -5, 1, 12,
-23, 24, -12, -10, 28, -17, -10, 13, 6, -14, 7, 7, -13, 1, 16, -30, 24, -11, -3,
17, -24, 23, -48, 23, -11, -26, 41, -39, 25, -17, 6, -11, -3, 6, -14, 6, -8, 21,
-27, 17, -2, 10, -28, 29, -2, -24, 25, -11, 8, -30, 13, -11, -26, 35, -43, 29,
-4, -19, 25, -33, 26, -32, 11, 1, -5, -5, 7, 13, -26, 29, -7, -17, 23, -31, 25,
-16, -5, 24, -31, 24, 1, -30, 16, -4, -29, 34, -38, 32, -22, 2, 10, -24, 30,
-30, 3, 15, -16, -6, 16, 8, -16, 7, 10, -15, 12, -15, 25, -25, 5, 11, -31, 35,
-24, -4, 19, -19, 12, -16, 5, 10, -28, 34, -11, -13, 28, -29, 17, -1, -1, 0,
-21, 30, -30, 8, 15, -23, 17, -2, 7, -8, -6, 22, -21, 17, 1, 0, -8, -2, 16, -30,
29, -14, -10, 27, -25, 18, -11, -1, 13, -22, 21, -12, -1, 15, -14, 15, -7, 8,
-4, -14, 27, -31, 19, -4, -6, 14, -15, 12, 12, -23, 20, -10, -7, 18, -31, 25,
-19, 14, -10, 10, 4, -15, 16, -17, 22, -20, 11, 0, -16, 28, -32, 17, -6, -5, 15,
-20, 11, -2, -8, 8, 5, -19, 21, -18, 10, -1, -4, 20, -26, 18, -4, -9, 18, -15,
5, 5, 3, -14, 16, -2, -16, 18, -17, 11, -10, 2, 6, -9, 2, 7, -9, 11, -2, -4, 5,
2, 2, -12, 18, -5, -8, 7, 2, -1, -4, 9, -6, -2, 9, -14, 4, 6, -6, -2, 8, -2, -8,
8, 4, -14, 12, -2, -11, 12, -3, 2, -2, -9, 10, -11, 9, -6, -1, 5, -6, 11, -16,
18, -14, 1, 7, -6, -6, 4, 6, -16, 17, -5, -10, 13, -7, 5, -6, 7, -4, -5, 10, -2,
-5, 1, 9, -15, 21, -16, 5, 4, -9, 8, 1, -4, 0, 5, -5, 2, 2, -6, 6, -4, -2, 7,
-10, 7, -3, 4, -10, 8, -9, 8, -2, -1, 6, -11, 17, -14, 4, 4, -10, 9, -2, -7, 7,
-6, 0, 6, -8, 4, -3, -1, 7, -8, 8, -5, 1, 4, -8, 7, 3, -11, 6, 3, -11, 13, -4,
-9, 15, -13, 4, 3, -9, 13, -14, 9, 2, -11, 13, -10, 0, 7, -8, 5, -5, 7, -1, -6,
7, -7, 2, -1, 6, -7, -4, 12, -14, 7, -2, 3, -6, 2, 4, -13, 17, -11, 1, 6, -4,
-3, 4, -5, 2, 1, -1, 1, -9, 12, -8, 0, 6, -12, 10, -8, 5, -4, -3, 11, -17, 13,
-6, 3, -6, 2, 6, -12, 12, -10, 6, 2, -5, 0, -2, 10, -9, 1, 4, -2, -7, 9, -3, -3,
3, -4, 8, -8, 8, -12, 8, -2, -4, 9, -10, 9, -10, 3, 5, -12, 9, -2, -6, 9, -7, 3,
-2, -3, 4, -8, 8, -4, -3, 6, -3, 0, -3, 7, -6, 1, 1, -5, 6, -6, 3, 1, -6, 9, -9,
6, -2, -4, 6, -5, 1, 2, -5, 3, -1, -2, 4, -7, 7, -7, 5, -2, 3, -5, -2, 9, -12,
7, -1, -3, 7, -10, 7, -2, -5, 7, -10, 8, -6, 3, 0, -4, 6, -5, -2, 6, -3, -2, 4,
-2, 0, 0, 2, -4, -2, 7, -8, 3, -1, 1, -3, -1, 5, -9, 9, -8, 6, -4, -2, 6, -8, 8,
-3, -5, 7, -6, 2, -3, 0, 2, -7, 7, -6, 1, 4, -4, -2, 6, -4, 0, 1, -2, -1, -2, 7,
-7, 3, 0, -1, -2, 0, 5, -8, 7, -5, 2, 1, -2, 3, -5, 5, -2, -3, 4, -1, -4, 4, -1,
-1, -1, 4, -6, 1, 4, -5, 2, 0, -2, 2, -1, 2, -2, -1, 6, -7, 3, -1, -3, 3, -1,
-3, 2, 0, 0, 0, -5, 5, -1, -4, 3, -2, -2, 2, 0, -1, -1, 2, 2, -5, 3, -1, -3, 6,
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

#endif /* closedhat_H_ */
