mattybrad/drumkid/arduino/1.1/drumkid/rim.h

#ifndef rim_H_
#define rim_H_
 
#if ARDUINO >= 100
#include "Arduino.h"
#else
#include "WProgram.h"
#endif
#include "src/MozziDK/src/mozzi_pgmspace.h"
 
#define rim_NUM_CELLS 427
#define rim_SAMPLERATE 16384
 
CONSTTABLE_STORAGE(int8_t) rim_DATA [] = {1, -1, 3, -7, -10, 2, 5, 3, 5, -2,
-43, -34, -29, -12, 38, 50, 36, 44, -12, -37, -26, -15, -15, 14, 62, 57, 34,
-47, -27, -18, -16, -13, 17, 63, 34, 43, -6, -97, -42, -30, -3, 45, 24, 32, 9,
20, -37, -67, -46, -20, 25, 22, 19, 20, -17, -42, -26, -22, -10, -5, 9, 23, 12,
13, 14, 17, 14, 16, 11, 42, 59, 41, -1, -83, -49, -16, 12, 34, 21, 17, 6, 0, -9,
-20, -35, -20, -21, -19, -20, -14, -29, -46, -32, -21, -6, 4, 15, 21, 28, 31,
33, 30, 30, 26, 22, 19, 18, 13, 7, -4, -8, -3, 3, 22, 17, 7, -3, -11, -18, -25,
-29, -30, -30, -28, -26, -22, -23, -31, -26, -17, -5, 4, 14, 21, 25, 29, 31, 30,
28, 26, 22, 17, 13, 10, 5, 2, 0, -2, -3, 1, 5, 7, 4, -5, -10, -15, -19, -21,
-23, -22, -21, -20, -20, -22, -18, -14, -7, 0, 5, 11, 16, 19, 20, 21, 21, 21,
19, 15, 13, 10, 7, 5, 2, 0, -1, -2, -3, -3, -3, -4, -4, -5, -7, -8, -10, -11,
-12, -13, -14, -14, -13, -11, -9, -5, -1, 2, 5, 7, 10, 12, 12, 13, 13, 12, 11,
9, 8, 6, 4, 2, 1, 0, -1, -1, -3, -3, -4, -4, -5, -4, -6, -6, -7, -7, -7, -7, -8,
-6, -6, -4, -3, -1, 0, 2, 3, 4, 5, 7, 6, 7, 7, 6, 6, 5, 4, 4, 2, 2, 1, 0, 0, -2,
-1, -2, -3, -2, -3, -4, -4, -4, -4, -5, -4, -4, -4, -4, -3, -2, -1, 0, 1, 2, 2,
4, 4, 4, 3, 4, 4, 4, 4, 4, 3, 2, 1, 2, 1, 1, 0, -1, -1, -2, -2, -2, -3, -2, -4,
-3, -3, -3, -3, -3, -2, -2, -2, -1, 0, 1, 1, 2, 3, 2, 3, 3, 3, 3, 3, 2, 2, 2, 2,
1, 1, 1, 1, 0, -1, -1, -1, -2, -1, -2, -2, -2, -2, -3, -2, -2, -2, -1, -1, -1,
0, 1, 1, 1, 1, 1, 1, 1, 2, 2, 1, 1, 1, 2, 1, 1, 0, 1, 0, 0, -1, 0, -1, -2, -1,
-1, -1, 0, 0, -1, 0, -1, 1, 0, 1, 0, 1, 1, 0, 0, 1, 0, 0, 0, -1, 0, 0, 0, 0, 1,
0, -1, -1, 0, -1, 0, 0, 0, 0, 0, -1, 0, 0, 1, 0, -1, -1, 1, 0, 0, 0, 0, 0, 0, 0,
};

#endif /* rim_H_ */
