mattybrad/drumkid/arduino/rp2040/dk2040_1/sample0.h

#ifndef sample0_H_
#define sample0_H_
 
#if ARDUINO >= 100
#include "Arduino.h"
#else
#include "WProgram.h"
#endif
#include <mozzi_pgmspace.h>
 
#define sample0_NUM_CELLS 6013
#define sample0_SAMPLERATE 16384
 
CONSTTABLE_STORAGE(int8_t) sample0_DATA [] = {0, 2, 18, 33, 44, 54, 61, 69, 75,
82, 86, 90, 93, 95, 98, 101, 101, 101, 98, 94, 88, 83, 77, 71, 65, 58, 51, 44,
37, 29, 22, 15, 7, -2, -9, -15, -23, -30, -37, -45, -51, -58, -65, -71, -77,
-83, -88, -94, -99, -104, -108, -112, -116, -119, -123, -125, -127, -127, -128,
-128, -128, -127, -126, -126, -125, -123, -123, -122, -120, -118, -116, -114,
-111, -108, -104, -101, -97, -93, -88, -83, -80, -73, -69, -64, -58, -52, -46,
-40, -34, -27, -21, -15, -9, -4, 2, 5, 11, 13, 17, 21, 24, 27, 30, 32, 35, 37,
39, 41, 44, 46, 47, 48, 50, 51, 53, 55, 57, 57, 58, 60, 60, 62, 63, 64, 65, 66,
67, 67, 68, 68, 69, 70, 70, 71, 71, 71, 71, 73, 73, 73, 73, 73, 74, 74, 74, 74,
74, 74, 73, 73, 74, 74, 72, 72, 73, 72, 71, 71, 71, 70, 70, 69, 69, 68, 67, 66,
67, 66, 64, 64, 64, 62, 61, 60, 60, 59, 58, 57, 57, 55, 54, 53, 52, 50, 50, 49,
47, 46, 44, 45, 43, 42, 40, 40, 38, 37, 35, 34, 33, 31, 29, 29, 28, 26, 25, 23,
22, 19, 18, 17, 16, 14, 13, 12, 9, 8, 6, 4, 3, 1, -1, -2, -3, -6, -7, -9, -11,
-13, -15, -17, -19, -20, -23, -25, -28, -29, -31, -33, -36, -38, -41, -42, -45,
-46, -49, -52, -54, -56, -58, -61, -64, -65, -67, -69, -72, -74, -77, -78, -80,
-83, -84, -86, -88, -90, -92, -94, -96, -98, -100, -100, -103, -104, -106, -107,
-109, -110, -111, -112, -113, -115, -116, -117, -118, -119, -118, -119, -120,
-120, -121, -121, -122, -122, -122, -122, -122, -121, -121, -121, -121, -120,
-119, -118, -118, -117, -117, -114, -114, -112, -110, -107, -106, -104, -102,
-100, -99, -96, -94, -92, -89, -88, -85, -82, -80, -77, -74, -72, -70, -66, -64,
-61, -58, -56, -53, -50, -47, -45, -42, -39, -36, -34, -30, -29, -24, -23, -19,
-18, -14, -12, -9, -6, -5, -2, 1, 3, 7, 8, 12, 14, 17, 19, 21, 24, 27, 28, 30,
32, 35, 38, 39, 41, 44, 46, 48, 50, 52, 54, 55, 58, 60, 62, 63, 65, 67, 68, 70,
71, 73, 75, 76, 77, 79, 80, 82, 83, 85, 86, 87, 89, 90, 90, 92, 94, 94, 96, 96,
98, 98, 99, 99, 100, 101, 102, 102, 102, 104, 104, 105, 105, 105, 105, 106, 106,
107, 106, 107, 107, 107, 107, 107, 106, 107, 106, 105, 106, 105, 105, 105, 105,
104, 103, 103, 103, 102, 101, 101, 101, 100, 98, 98, 97, 97, 95, 95, 94, 93, 92,
90, 90, 89, 88, 86, 85, 83, 83, 82, 79, 78, 77, 76, 74, 73, 71, 70, 69, 68, 65,
65, 62, 61, 59, 57, 55, 54, 53, 51, 49, 47, 45, 44, 42, 40, 38, 36, 34, 32, 30,
28, 26, 25, 23, 21, 19, 17, 15, 13, 11, 9, 7, 6, 3, 1, -1, -3, -5, -7, -10, -11,
-14, -16, -18, -20, -22, -24, -26, -28, -31, -33, -35, -37, -40, -43, -44, -46,
-50, -51, -53, -56, -58, -60, -63, -65, -67, -69, -71, -74, -76, -77, -80, -82,
-83, -85, -87, -90, -91, -92, -95, -96, -98, -100, -102, -102, -105, -107, -108,
-108, -109, -111, -112, -114, -115, -115, -116, -118, -118, -118, -119, -120,
-120, -120, -121, -120, -121, -121, -121, -121, -121, -121, -120, -120, -120,
-120, -119, -119, -117, -117, -116, -115, -114, -113, -112, -110, -109, -107,
-107, -105, -103, -102, -100, -98, -96, -94, -93, -90, -89, -87, -85, -82, -80,
-78, -75, -73, -71, -69, -66, -64, -61, -59, -57, -54, -52, -49, -47, -44, -42,
-40, -37, -35, -32, -31, -28, -26, -22, -21, -18, -15, -13, -11, -9, -6, -4, -1,
0, 2, 4, 8, 9, 12, 13, 16, 18, 20, 23, 25, 27, 29, 31, 32, 34, 37, 39, 40, 43,
44, 46, 47, 49, 51, 53, 54, 56, 58, 58, 61, 62, 64, 66, 66, 68, 69, 71, 72, 74,
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

#endif /* sample0_H_ */
