mattybrad/drumkid/arduino/rp2040/dk2040_1/sample2.h

#ifndef sample2_H_
#define sample2_H_
 
#if ARDUINO >= 100
#include "Arduino.h"
#else
#include "WProgram.h"
#endif
#include <mozzi_pgmspace.h>
 
#define sample2_NUM_CELLS 2840
#define sample2_SAMPLERATE 16384
 
CONSTTABLE_STORAGE(int8_t) sample2_DATA [] = {2, -3, 9, 17, -13, -23, -22, -8,
2, 11, 12, 13, 18, 12, 5, 1, 4, 1, -2, -12, -12, -9, -17, -22, -22, -17, -9, -5,
5, 10, 3, -3, -3, 10, 23, 21, 11, -1, -6, -9, -7, 1, 5, 8, 14, 17, 21, 22, 13,
14, 18, 21, 15, 7, -1, -5, -7, -29, -23, -11, -26, -10, -6, -24, -9, -3, -23,
-15, 13, -15, -30, -14, -17, -19, -18, -14, -4, -1, -4, -4, -11, -30, -7, 25,
12, 0, -1, -22, -21, 18, 41, 34, 20, 28, 40, 36, 27, 24, 19, 17, 15, 10, 9, 8,
-14, -24, -13, -2, 2, -18, -13, -9, -18, -5, 3, 9, 17, 19, 20, 25, 23, 11, 5, 5,
6, -13, -3, 5, -14, -30, -16, 0, -3, 26, 17, 23, 45, 30, 25, 30, 1, -7, 9, 36,
4, -10, 20, -19, -34, -55, -63, -56, -42, -19, -24, -14, -28, -67, -80, -62,
-63, -38, -7, -70, -109, -61, -33, -87, -103, -34, -7, -81, -76, 5, 4, -28, -33,
-10, 19, 32, 24, 34, 43, 46, 48, 42, 52, 48, 44, 45, 27, 43, 47, 33, 45, 51, 28,
18, 44, 55, 47, 37, 39, 43, 43, 28, 31, 29, 22, 23, 41, 41, 34, 41, 51, 24, -7,
7, 41, 13, -33, 23, 32, 27, 18, 0, 25, 27, 4, 24, 39, -49, -101, -60, -1, 4,
-48, 3, 8, -46, -60, -53, -44, -82, -88, -90, -87, -91, -107, -92, -58, -80,
-100, -83, -83, -56, -66, -94, -85, -90, -23, -35, -91, -77, -83, -71, -58, -29,
21, 6, -58, -39, 3, 36, -9, -31, 28, 43, 35, 41, 27, 35, 65, 58, 52, 43, 56, 64,
60, 54, 66, 66, 57, 51, 54, 67, 56, 47, 64, 71, 60, 44, 57, 64, 52, 41, 36, 40,
50, 59, 40, 41, 40, 25, -6, 12, 43, 14, -8, -1, 27, 57, 5, -50, 16, 34, -14,
-54, -47, 3, 23, -32, -51, -12, 17, -40, -100, -25, 25, -48, -99, -57, -27, -38,
-65, -63, -74, -63, -70, -75, -55, -65, -76, -81, -76, -69, 9, -5, -66, -40, -9,
-11, -42, -59, -3, -23, -74, -32, -24, -37, 10, 45, -2, -18, -28, 16, 42, 27,
12, 28, 35, -5, 34, 43, 21, 27, 48, 60, 45, 54, 56, 40, 49, 18, 22, 45, 48, 39,
36, 46, 36, 1, -13, 52, 28, 6, -13, -1, 29, -15, -1, 13, 11, -34, -26, 44, 57,
5, -27, 29, -17, -49, -6, 1, 37, 26, -3, -16, -21, 32, 34, -8, 9, 21, -10, -10,
-14, 5, 42, -6, -1, 25, 7, 9, 4, 32, 11, -33, -3, 28, 8, -23, 10, 33, 8, 25, 7,
11, 25, 33, 21, 1, 26, 13, 24, 20, 20, 12, 1, -11, -10, 45, 11, -1, 19, 32, 26,
8, 7, 10, 40, 27, 9, 6, 44, -8, -20, 35, 10, 9, 31, 48, 16, -17, -11, 13, 32,
12, 2, 15, -4, 7, -1, -19, 19, 14, 16, 13, -21, -6, -8, -5, 2, -19, 6, 4, -40,
-17, -10, -22, -22, -5, -9, -39, -29, 7, -23, -65, -40, -5, 0, -28, -28, -27,
-15, -11, -29, -42, -12, -35, -36, -24, -25, -4, -6, 6, 1, -25, -8, 22, 8, 8,
-17, 13, 33, 14, 3, -15, 2, 7, -9, 10, 16, 11, 46, 27, 10, 11, 2, 17, 40, 10,
-4, 8, -9, 24, 35, 5, 20, 42, 38, -5, -27, 13, 8, 24, 40, 19, 14, 26, 22, -2,
25, 26, 15, 6, 15, 32, 23, 14, 5, 2, 18, 35, -2, -4, 9, 4, 16, 16, -6, 8, 14, 2,
6, -7, -3, 2, 8, 5, 4, 3, -1, 4, 5, 5, -9, -17, 8, 16, 11, 4, -3, 11, 17, 14, 0,
4, 8, 11, 4, 11, 23, 11, 11, 8, 3, -6, 0, -8, 12, 16, 6, 16, 8, -7, 8, 30, -15,
-19, 1, 5, -1, -4, 8, 1, -17, -13, -1, -4, -7, -10, -9, -4, 2, -3, -4, -3, -20,
-27, 4, -3, -11, -2, -9, -12, -9, 5, -12, -33, -17, 4, -3, -18, -10, 3, 2, -4,
-5, -12, -8, -5, 10, 4, -17, -9, -5, 1, -6, -10, -12, -4, 6, 1, -5, 3, 2, -10,
5, 8, 7, 1, 8, 15, 2, 3, 12, 7, 0, 10, 15, 7, 2, 7, 5, 11, 13, 1, 4, 8, 18, 10,
-2, 8, 8, 12, 13, 2, 3, 8, 10, 12, 9, 11, 4, 1, 10, 13, 7, -4, -1, 11, 13, 5,
11, 14, 10, 16, 5, 4, 8, 3, 9, 6, 1, 4, 5, 6, -2, 0, 12, 6, -2, -7, 5, 5, -2, 5,
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

#endif /* sample2_H_ */
