mattybrad/drumkid/arduino/rp2040/dk2040_1/sample4.h

#ifndef sample4_H_
#define sample4_H_
 
#if ARDUINO >= 100
#include "Arduino.h"
#else
#include "WProgram.h"
#endif
#include <mozzi_pgmspace.h>
 
#define sample4_NUM_CELLS 2870
#define sample4_SAMPLERATE 16384
 
CONSTTABLE_STORAGE(int8_t) sample4_DATA [] = {0, -1, 1, -1, 0, -1, 1, 3, 6, 5,
4, 4, 3, 4, -84, -128, -105, -78, -57, -54, -48, -50, -47, -40, -35, -30, -22,
-16, -9, -1, 6, 13, 20, 26, 32, 38, 41, 47, 49, 54, 55, 58, 58, 61, 59, 60, 58,
52, 54, 54, 51, 49, 47, 47, 46, 46, 46, 46, 44, 45, 44, 44, 44, 43, 42, 44, 43,
42, 42, 42, 40, 42, 40, 41, 41, 41, 40, 40, 36, 31, 31, 33, 35, 34, 36, 30, 23,
23, 26, 28, 28, 19, 17, 18, 22, 19, 11, 11, 15, 16, 8, 5, 9, 9, 3, 0, 4, 2, -3,
-4, -1, -5, -10, -7, -7, -13, -14, -11, -14, -19, -17, -15, -23, -24, -19, -23,
-28, -25, -25, -31, -30, -27, -31, -36, -32, -32, -37, -39, -36, -36, -43, -42,
-39, -40, -46, -45, -42, -41, -47, -49, -48, -43, -44, -52, -52, -49, -45, -45,
-51, -53, -52, -50, -47, -46, -46, -51, -54, -52, -49, -49, -47, -47, -46, -46,
-45, -45, -45, -45, -45, -45, -49, -50, -47, -41, -39, -39, -40, -41, -41, -42,
-41, -40, -40, -40, -40, -39, -33, -30, -30, -32, -30, -24, -23, -24, -18, -18,
-14, -11, -10, -6, -4, -1, 2, 5, 8, 12, 14, 16, 19, 21, 25, 26, 29, 30, 33, 35,
36, 39, 39, 43, 41, 44, 45, 44, 48, 47, 45, 49, 51, 48, 44, 47, 51, 51, 48, 46,
45, 44, 43, 47, 51, 51, 48, 46, 45, 45, 45, 44, 44, 43, 43, 43, 42, 42, 42, 42,
41, 36, 32, 32, 34, 35, 36, 36, 36, 35, 34, 30, 25, 25, 27, 28, 30, 28, 21, 19,
19, 21, 24, 18, 14, 13, 16, 17, 11, 7, 10, 11, 8, 3, 4, 7, 4, -1, 0, 1, -2, -5,
-4, -4, -7, -10, -9, -8, -12, -13, -13, -14, -19, -18, -16, -19, -23, -22, -21,
-24, -25, -23, -25, -28, -29, -27, -29, -32, -33, -30, -31, -36, -37, -34, -33,
-37, -40, -38, -35, -36, -41, -42, -41, -38, -37, -41, -44, -43, -42, -40, -39,
-41, -46, -47, -45, -43, -41, -40, -40, -40, -40, -44, -47, -46, -45, -43, -42,
-41, -40, -40, -40, -39, -39, -38, -39, -38, -38, -38, -38, -38, -35, -30, -27,
-28, -29, -31, -31, -31, -25, -22, -22, -23, -20, -18, -16, -15, -12, -10, -7,
-6, -3, -1, 2, 4, 7, 9, 11, 14, 16, 18, 20, 22, 24, 27, 28, 30, 31, 33, 34, 35,
37, 39, 38, 41, 41, 40, 41, 43, 43, 41, 43, 46, 45, 43, 40, 40, 43, 46, 47, 46,
43, 42, 40, 41, 40, 41, 40, 39, 39, 39, 39, 38, 38, 37, 37, 37, 37, 37, 36, 36,
37, 35, 35, 34, 29, 26, 26, 27, 29, 29, 29, 29, 25, 21, 20, 21, 23, 23, 21, 16,
14, 16, 17, 17, 12, 9, 10, 12, 11, 7, 6, 6, 7, 4, 1, 1, 3, 1, -2, -3, -3, -4,
-7, -6, -7, -9, -11, -11, -10, -12, -14, -14, -14, -16, -18, -17, -18, -19, -22,
-22, -20, -23, -25, -24, -24, -26, -27, -28, -26, -28, -30, -32, -29, -29, -32,
-34, -34, -32, -31, -33, -36, -36, -35, -33, -33, -35, -38, -39, -38, -36, -35,
-33, -34, -36, -40, -41, -40, -38, -37, -35, -36, -34, -34, -34, -35, -33, -33,
-34, -32, -33, -32, -33, -32, -32, -32, -31, -31, -30, -31, -31, -30, -31, -28,
-24, -21, -22, -22, -23, -20, -18, -16, -16, -14, -11, -11, -9, -7, -5, -3, -1,
2, 3, 5, 8, 8, 11, 13, 16, 17, 18, 20, 22, 23, 25, 26, 28, 30, 30, 32, 33, 33,
34, 35, 36, 38, 36, 36, 38, 39, 38, 36, 38, 40, 41, 41, 39, 37, 37, 35, 36, 35,
36, 38, 42, 42, 40, 40, 38, 37, 36, 36, 35, 35, 35, 35, 34, 29, 27, 27, 26, 28,
30, 29, 29, 29, 29, 29, 27, 23, 21, 20, 21, 22, 24, 22, 20, 17, 16, 15, 17, 16,
15, 12, 11, 11, 12, 10, 8, 7, 8, 7, 6, 4, 4, 4, 3, -1, 0, -1, -1, -3, -5, -4,
-5, -6, -9, -9, -8, -10, -12, -11, -12, -14, -15, -15, -15, -16, -18, -19, -18,
-19, -21, -21, -21, -22, -22, -25, -25, -24, -24, -26, -27, -28, -27, -26, -29,
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
};

#endif /* sample4_H_ */
