mattybrad/drumkid/arduino/rp2040/dk2040_1/sample1.h

#ifndef sample1_H_
#define sample1_H_
 
#if ARDUINO >= 100
#include "Arduino.h"
#else
#include "WProgram.h"
#endif
#include <mozzi_pgmspace.h>
 
#define sample1_NUM_CELLS 1527
#define sample1_SAMPLERATE 16384
 
CONSTTABLE_STORAGE(int8_t) sample1_DATA [] = {-1, 2, -1, 6, -3, -3, 1, -3, -2,
7, -8, 2, 5, -5, -4, 9, -6, 3, -3, -10, 24, -17, 1, 5, -13, 19, -19, 8, 4, -21,
25, -20, 9, -6, 2, 2, -2, -1, -2, 8, -7, 3, 0, -3, 0, 4, -8, 13, -7, -1, 5, -4,
3, -1, -5, 8, -7, 0, 0, 13, -19, 8, -4, -2, 6, -12, 14, -21, 16, -8, -11, 15,
-3, -15, 24, -26, 18, -14, -10, 47, -42, 20, -10, -2, 15, -13, -6, 10, 0, -19,
35, -50, 41, -16, -19, 38, -60, 46, -40, 13, 8, -21, -6, 13, 1, -29, 43, -36,
16, -9, 5, 5, -44, 46, -45, 20, -4, -7, -3, 13, 10, -32, 32, -36, 37, -43, 0,
-5, -35, 34, -30, 10, -12, 19, -16, -4, 31, -50, 26, -21, 11, -23, 24, 5, -32,
25, -10, -4, -4, 22, -39, 46, -32, 7, 8, -4, -1, -16, 23, -29, 18, -5, 2, 12,
-23, 24, -12, -11, 29, -18, -9, 14, 6, -15, 8, 6, -11, 0, 17, -31, 25, -11, -2,
17, -23, 23, -48, 23, -12, -26, 41, -40, 24, -16, 6, -11, -5, 7, -15, 7, -8, 21,
-26, 18, -3, 11, -28, 30, -3, -23, 25, -11, 9, -31, 14, -11, -25, 35, -42, 28,
-4, -20, 25, -34, 26, -33, 12, 0, -5, -6, 8, 12, -25, 29, -7, -17, 23, -31, 25,
-16, -5, 25, -32, 23, 0, -28, 16, -4, -30, 35, -38, 34, -23, 3, 10, -24, 29,
-29, 3, 16, -16, -6, 16, 8, -16, 6, 11, -15, 12, -15, 26, -27, 6, 10, -30, 34,
-23, -5, 20, -20, 12, -16, 5, 8, -29, 34, -11, -14, 29, -29, 16, -1, -2, 0, -21,
30, -31, 8, 14, -22, 16, -2, 6, -7, -7, 22, -22, 16, 0, 0, -9, -2, 15, -29, 29,
-13, -10, 27, -25, 18, -11, -2, 13, -22, 21, -13, -1, 15, -13, 15, -8, 8, -4,
-14, 27, -32, 20, -4, -5, 14, -15, 12, 12, -22, 20, -10, -8, 19, -32, 25, -20,
15, -11, 11, 4, -14, 15, -17, 21, -19, 10, 0, -16, 29, -32, 17, -6, -5, 16, -19,
10, -2, -7, 8, 5, -20, 21, -19, 11, -1, -3, 19, -27, 17, -4, -10, 18, -14, 4, 5,
3, -14, 17, -1, -17, 17, -18, 11, -10, 4, 5, -8, 1, 7, -10, 11, -2, -3, 4, 1, 2,
-11, 18, -6, -8, 6, 3, 0, -3, 9, -5, -2, 9, -16, 5, 5, -5, -2, 8, -3, -7, 8, 5,
-14, 12, -1, -11, 11, -4, 1, -1, -9, 11, -11, 9, -6, -1, 6, -7, 11, -16, 18,
-14, 2, 7, -5, -7, 4, 5, -16, 16, -5, -9, 13, -7, 4, -6, 7, -4, -6, 11, -2, -6,
1, 8, -15, 22, -18, 7, 3, -10, 7, 1, -4, 0, 5, -5, 2, 2, -5, 7, -4, -2, 8, -9,
7, -2, 4, -10, 10, -9, 7, -2, -1, 6, -12, 16, -13, 3, 3, -10, 8, -2, -6, 8, -6,
1, 5, -8, 3, -3, -1, 7, -10, 7, -5, 1, 3, -8, 7, 4, -12, 5, 2, -11, 13, -4, -8,
14, -13, 4, 3, -9, 14, -14, 8, 1, -11, 12, -9, 0, 8, -8, 4, -5, 7, -1, -5, 8,
-6, 1, 0, 6, -7, -3, 11, -13, 8, -1, 4, -5, 2, 4, -13, 16, -12, 1, 5, -4, -3, 5,
-5, 3, 2, 0, 1, -9, 12, -7, 0, 6, -11, 10, -7, 5, -4, -4, 11, -17, 14, -6, 3,
-7, 3, 5, -11, 12, -11, 5, 2, -5, 0, -2, 10, -9, 1, 4, -2, -7, 9, -2, -4, 2, -4,
8, -9, 9, -12, 8, -2, -5, 8, -10, 10, -9, 3, 5, -11, 9, -1, -6, 9, -7, 3, -1,
-3, 5, -6, 7, -3, -3, 6, -3, 0, -3, 6, -6, 1, 1, -5, 7, -6, 3, 1, -7, 9, -9, 6,
-1, -4, 7, -6, 2, 2, -4, 3, -1, -2, 5, -8, 7, -8, 5, -3, 3, -4, -1, 8, -11, 8,
-3, -3, 6, -11, 7, -2, -5, 7, -10, 8, -6, 3, -1, -4, 6, -5, -2, 5, -3, -3, 3,
-2, -1, 0, 3, -5, -1, 7, -8, 3, -1, 0, -2, -1, 5, -9, 9, -9, 6, -3, -2, 4, -8,
8, -2, -4, 7, -4, 2, -1, 0, 3, -7, 7, -6, 1, 3, -4, -2, 7, -5, 0, 1, -1, -1, -2,
7, -7, 4, 0, -2, -1, 0, 5, -8, 7, -5, 0, 2, -3, 3, -5, 6, -2, -4, 3, -1, -4, 3,
-1, 0, 0, 3, -6, 1, 4, -5, 3, 0, -4, 1, -1, 2, -2, -2, 6, -8, 3, 0, -2, 3, -2,
-1, 2, 0, 0, 0, -4, 5, 0, -3, 4, -2, -2, 2, 1, 0, -1, 1, 2, -5, 3, -1, -3, 6,
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

#endif /* sample1_H_ */
